fabiano-dot/Estacao_Meteorologica/EstacaoMeteorologica/DocumentacaoFinalDoProjeto/Hardware/WCM/assets/3d_B.cu.png

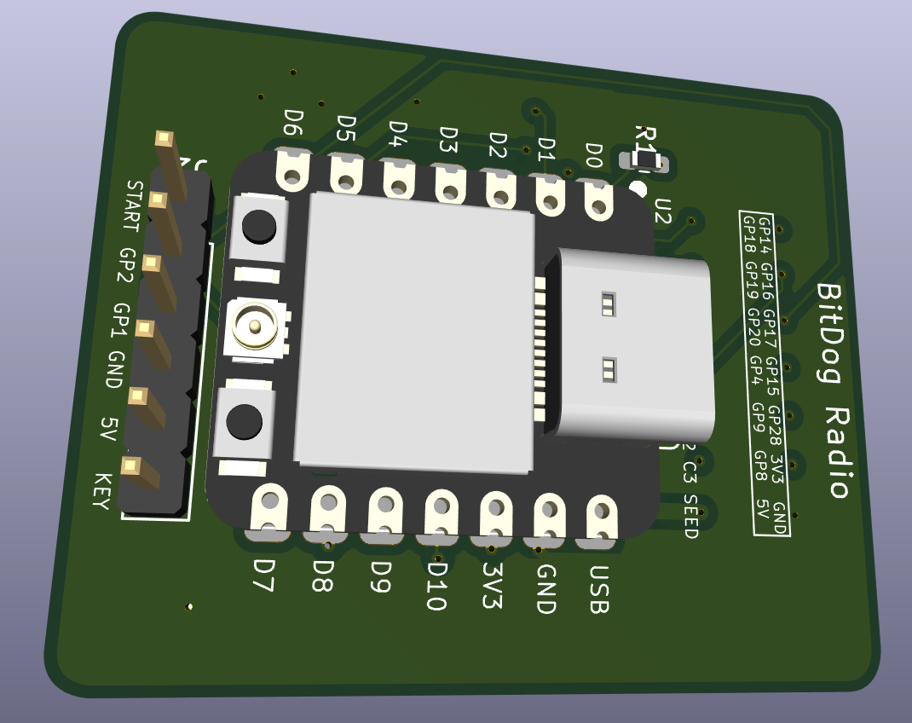
EstacaoMeteorologica/DocumentacaoFinalDoProjeto/Hardware/WCM/assets/3d_B.cu.png
