fabiano-dot/Estacao_Meteorologica/EstacaoMeteorologica/DocumentacaoFinalDoProjeto/Hardware/WCM/assets/F.cu.png

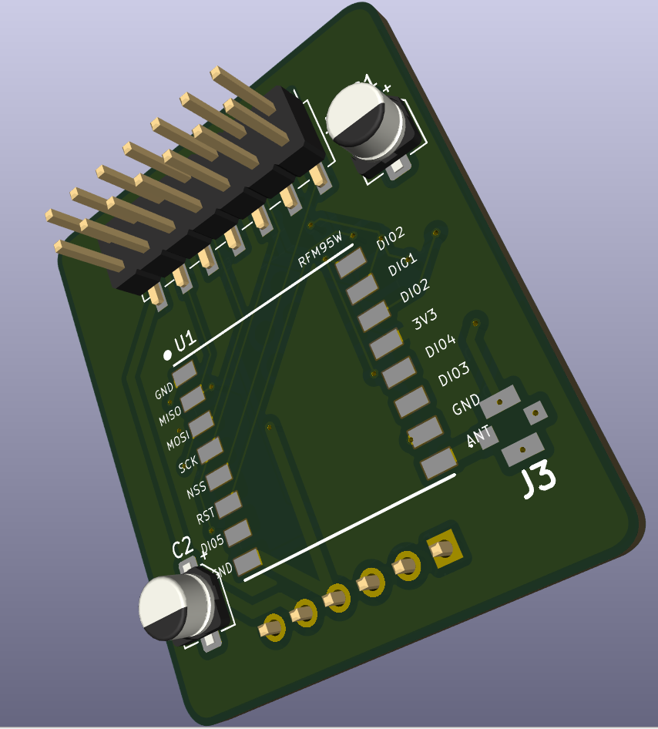
EstacaoMeteorologica/DocumentacaoFinalDoProjeto/Hardware/WCM/assets/F.cu.png
