fabiano-dot/Estacao_Meteorologica/EstacaoMeteorologica/DocumentacaoFinalDoProjeto/Hardware/WCM/assets/WCM_v1D.jpg

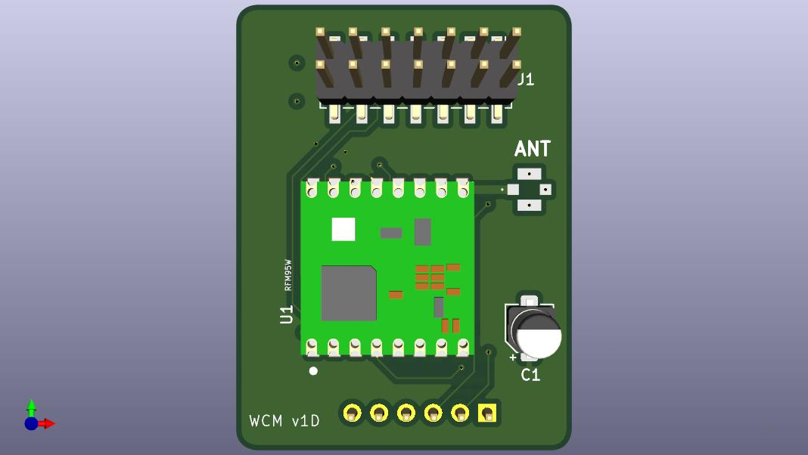
EstacaoMeteorologica/DocumentacaoFinalDoProjeto/Hardware/WCM/assets/WCM_v1D.jpg
