fabiano-dot/Estacao_Meteorologica/EstacaoMeteorologica/DocumentacaoFinalDoProjeto/Software/Main_Board/docs/html/aq__data_8h__dep__incl.png

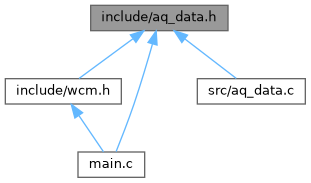
EstacaoMeteorologica/DocumentacaoFinalDoProjeto/Software/Main_Board/docs/html/aq__data_8h__dep__incl.png
