fabiano-dot/Estacao_Meteorologica/infraestrutura_local/figures/20260616_16h52m58s_grim.png

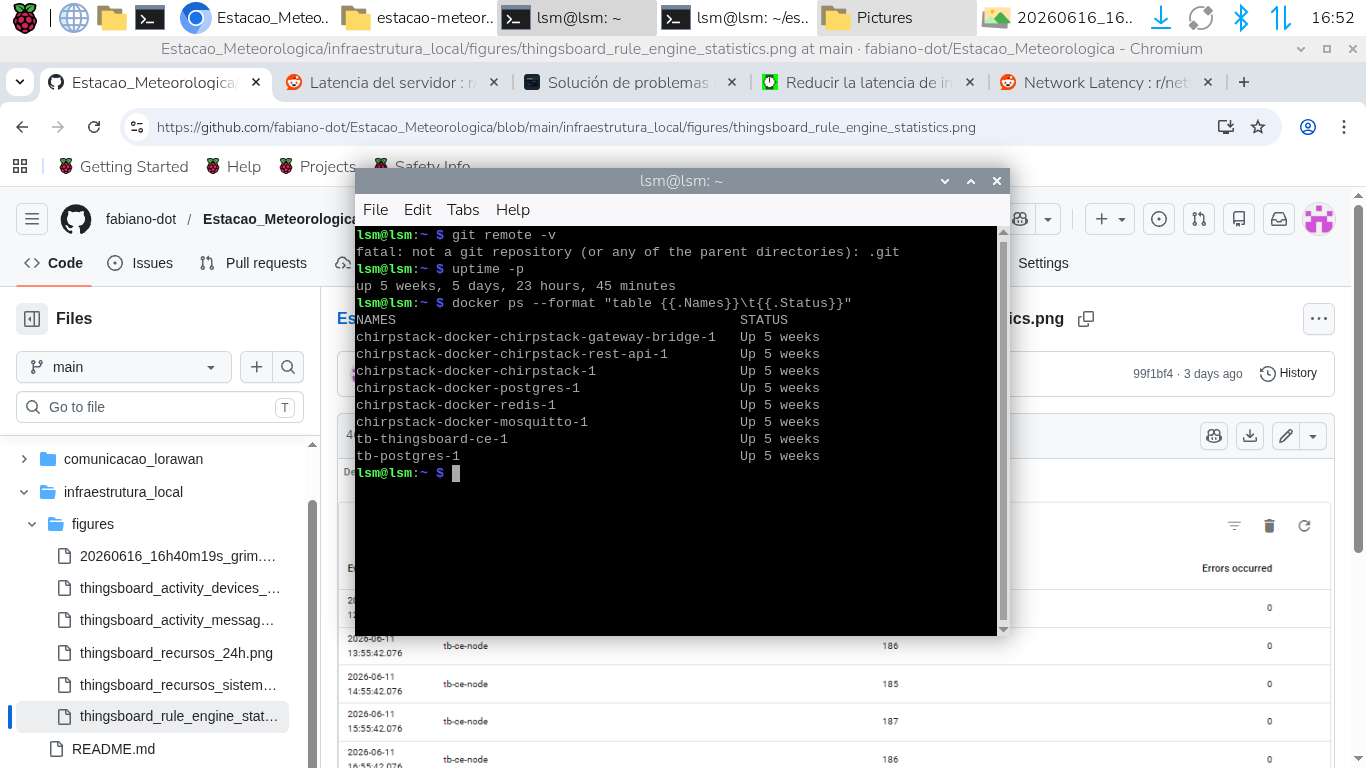
infraestrutura_local/figures/20260616_16h52m58s_grim.png
