fabiano-dot/Estacao_Meteorologica/infraestrutura_local/figures/20260616_17h09m34s_grim.png

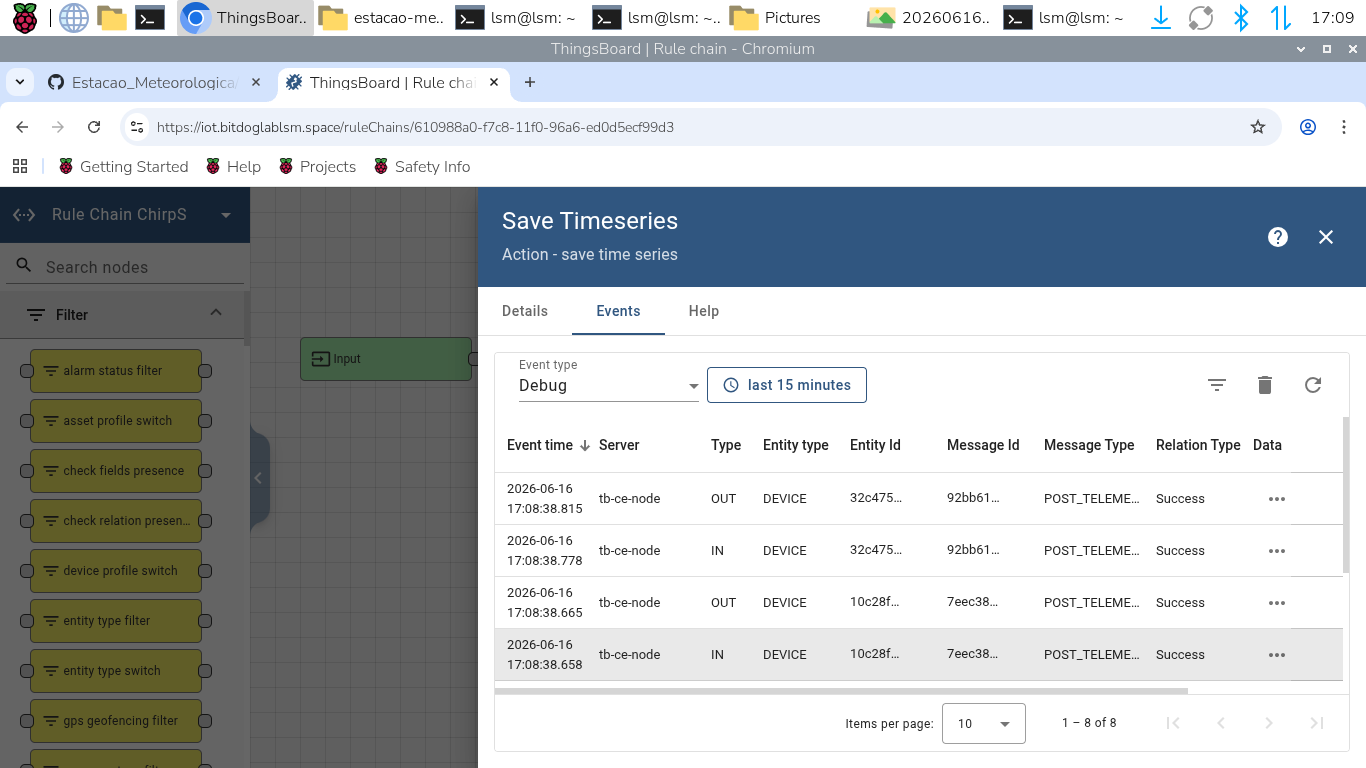
infraestrutura_local/figures/20260616_17h09m34s_grim.png
