fabiano-dot/Estacao_Meteorologica/infraestrutura_local/figures/20260616_18h24m54s_grim.png

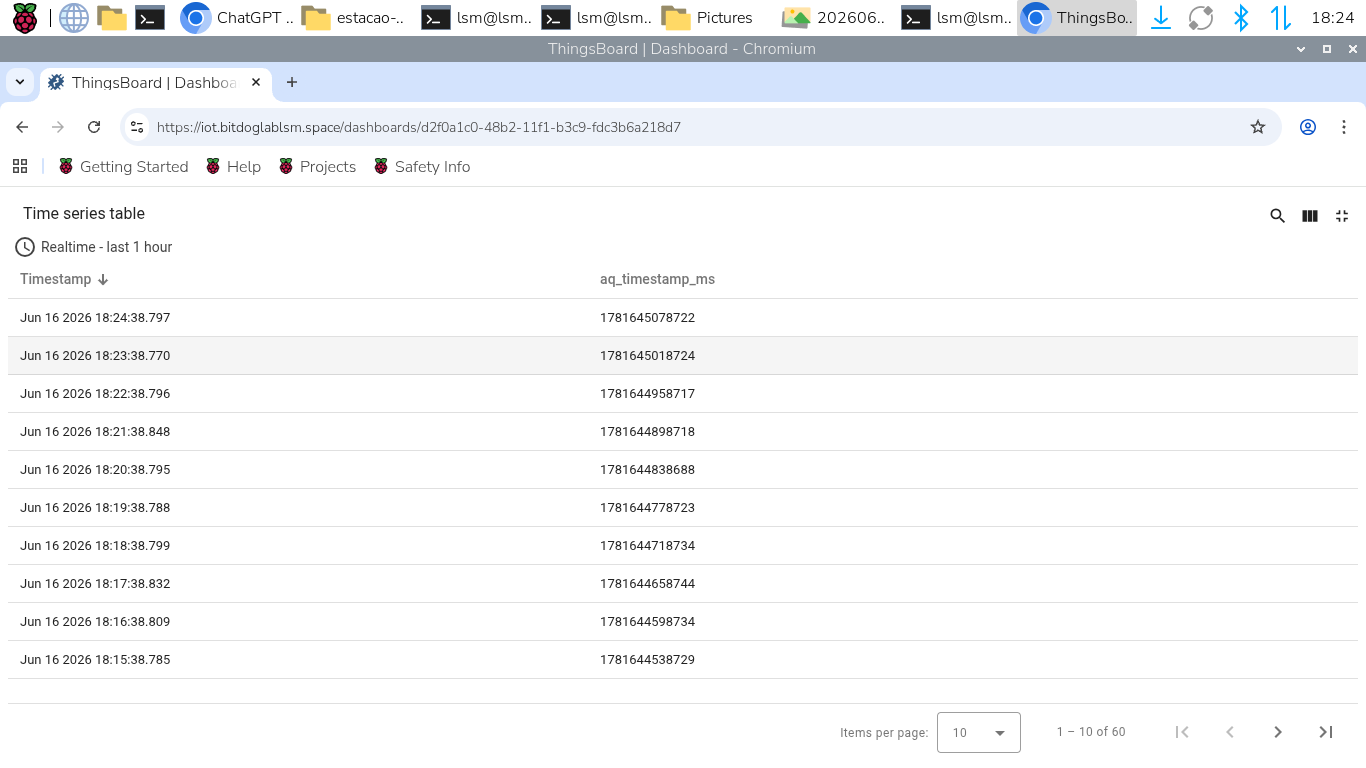
infraestrutura_local/figures/20260616_18h24m54s_grim.png
