fabiano-dot/Estacao_Meteorologica/EstacaoMeteorologica/DocumentacaoFinalDoProjeto/Software/WCM/lmic_abp_00/config.cpp

#include "config.h"


const char * SETUP_MSG = 
    "\n\n"
    "********** WCM **********\n"
    "* - Versão 0.00.08      *\n"
    "* - 07/04/2026          *\n"
    "* - Build: 0008         *\n"
    "*************************\n"
    "\n"
    "\n"
    "Comands:\n"
    "  - L  ==> LoRa\n"
    "  - A  ==> LoRaWAN ABP\n"
    "  - O  ==> LoRaWAN OTAA\n"
    "\n"
    "\n"
    "Formatos:\n"
    "- LoRa:\n"
    "    address     size\n"
    "  - (0x00)       1 Byte:  'L'\n"
    "  - (0x01)       1 Byte:  SPACE\n"
    "  - (0x02)       2 Bytes: Channel (00 a 63 ==> 0x00 a 0x3F)\n"
    "  - (0x04)       1 Byte:  SPACE\n"
    "  - (0x05)       2 Byte:  SF (07 a 12 ==> 0x07 a 0x0C)\n"
    "  - (0x07)       1 Byte:  SPACE\n"
    "  - (0x08)     2*x Bytes: HEXA Message(x Bytes)\n"
    "  - (0x09+(2*x)) 1 Byte:  '\\n'\n"
    "  Example: L ch sf -Message\\n\n"
    "  Example: L 05 07 12345678\\n\n"
    "\n"
    "\n"
    "- LoRaWAN ABP:\n"
    "    address     size\n"
    "  - (0x00)       1 Byte:  'A'\n"
    "  - (0x01)       1 Byte:  SPACE\n"
    "  - (0x02)       2 Bytes: Channel (00 a 63 ==> 0x00 a 0x3F, ou 0xFD(Auto 0-7), 0xFE(Auto 8-15), 0xFF(Auto 0-15))\n"
    "  - (0x04)       1 Byte:  SPACE\n"
    "  - (0x05)       2 Byte:  SF (07 a 12 ==> 0x07 a 0x0C)\n"
    "  - (0x07)       1 Byte:  SPACE\n"
    "  - (0x08)       8 Bytes  abp_devaddr(4 bytes)\n"
    "  - (0x10)       1 Byte:  SPACE\n"
    "  - (0x11)       4 Bytes  fcnt(2 bytes)\n"
    "  - (0x15)       1 Byte:  SPACE\n"
    "  - (0x16)      32 Bytes: appskey(16 bytes)\n"
    "  - (0x36)       1 Byte:  SPACE\n"
    "  - (0x37)      32 Bytes: nwkskey(16 bytes)\n"
    "  - (0x57)       1 Byte:  SPACE\n"
    "  - (0x58)     2*x Bytes: HEXA Message(x Bytes)\n"
    "  - (0x59+(2*x)) 1 Byte:  '\\n'\n"
    "  Example  : A ch sf devaddr  fcnt ------------appskey------------- ------------nwkskey------------- -Message--\\n\n"
    "  Example 1: A 05 07 12345678 4321 00112233445566778899AABBCCDDEEFF FFEEDDCCBBAA99887766554433221100 0987654321\\n\n"
    "   ==> HEX : 40 78 56 34 12 00 21 43 01 BE 8C 98 F4 DA 17 05 54 8E\n"
    "      Test : lora-packet-decode --appkey 00112233445566778899AABBCCDDEEFF --nwkkey FFEEDDCCBBAA99887766554433221100 --hex 407856341200214301BE8C98F4DA1705548E\n"

    "  Example 1: A 05 07 12345678 0123 00112233445566778899AABBCCDDEEFF FFEEDDCCBBAA99887766554433221100 07994509EF247AF4976157E876D9C710E1\\n\n"
    "   ==> HEX : 40 78 56 34 12 00 23 01 01 84 7C F5 0A A5 C3 CF 81 BA C1 A4 67 6B 47 3F 29 7D 19 43 8D 9A\n"
    "      Test : lora-packet-decode --appkey 00112233445566778899AABBCCDDEEFF --nwkkey FFEEDDCCBBAA99887766554433221100 --hex 407856341200230101847CF50AA5C3CF81BAC1A4676B473F297D19438D9A\n"
    "\n"
    "\n"
    "- LoRaWAN OTAA:\n"
    "    address     size\n"
    "  - (0x00)       1 Byte:  'O'\n"
    "  - (0x01)       1 Byte:  SPACE\n"
    "  - (0x02)       2 Bytes: Channel (00 a 63 ==> 0x00 a 0x3F)\n"
    "  - (0x04)       1 Byte:  SPACE\n"
    "  - (0x05)       2 Byte:  SF (07 a 12 ==> 0x07 a 0x0C)\n"
    "  - (0x07)       1 Byte:  SPACE\n"
    "  - (0x08)       8 Bytes  devaddr(4 bytes)\n"
    "  - (0x10)       1 Byte:  SPACE\n"
    "  - (0xxx)      16 Bytes  DevEui(8 bytes)\n"
    "  - (0xxx)      16 Bytes: AppEui(8 bytes)\n"
    "  - (0xxx)       1 Byte:  SPACE\n"
    "  - (0xxx)      32 Bytes: AppKey(16 bytes)\n"
    "  - (0xxx)       1 Byte:  SPACE\n"
    "  - (0xxx)     2*x Bytes: HEXA Message(x Bytes)\n"
    "  - (0xxx+(2*x)) 1 Byte:  '\\n'\n"
    "  Example: O ch sf -----DevEui----- -----AppEui----- -------------AppKey------------- -Message--\\n\n"
    "  Example: O 05 07 0011223344556677 FFEEDDCCBBAA9988 00112233445566778899AABBCCDDEEFF 1234567890\\n\n"
    "\n"
    "\n"
    "Return: 0      ==> OK\n"
    "        ERROR: ==> Error msg\n";
 
